CalebO-B/Roll-Only-Canard-Prototype--Controls-Lab-Final-Project-/STL Files/(2in gear) Pinion No edits.STL

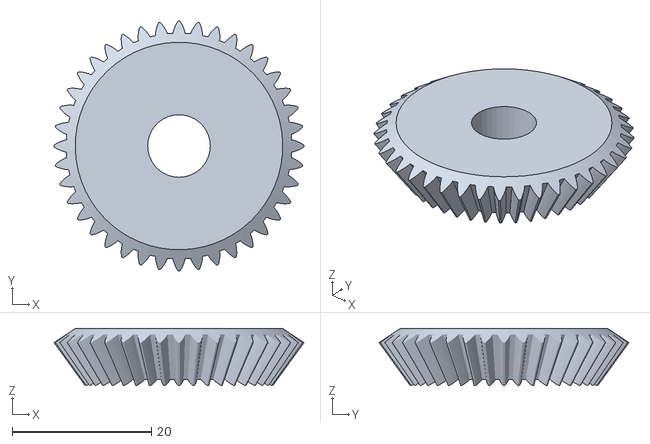
[picture p23: CAD file, 2025-02-27]
STL Files/(2in gear) Pinion No edits.STL
35.9 x 35.9 x 8.20
