CalebO-B/Roll-Only-Canard-Prototype--Controls-Lab-Final-Project-/Solidworks Files/Servo.SLDPRT

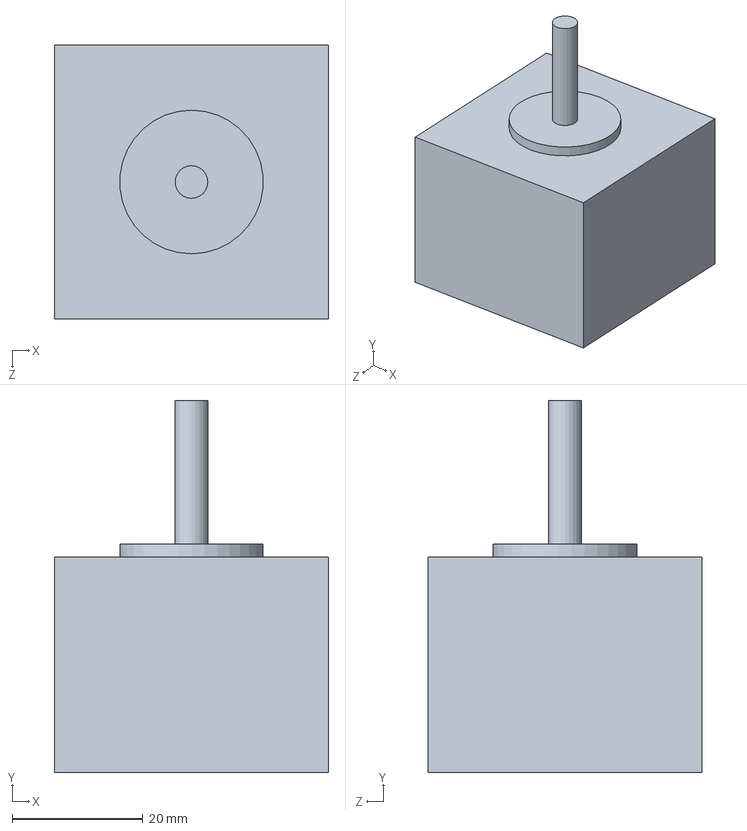
[picture p24: CAD file, 2025-02-27]
Solidworks Files/Servo.SLDPRT
42.0 x 57.0 x 42.0 mm
