CalebO-B/Roll-Only-Canard-Prototype--Controls-Lab-Final-Project-/STL Files/(2in gear) Gear No edits.STL

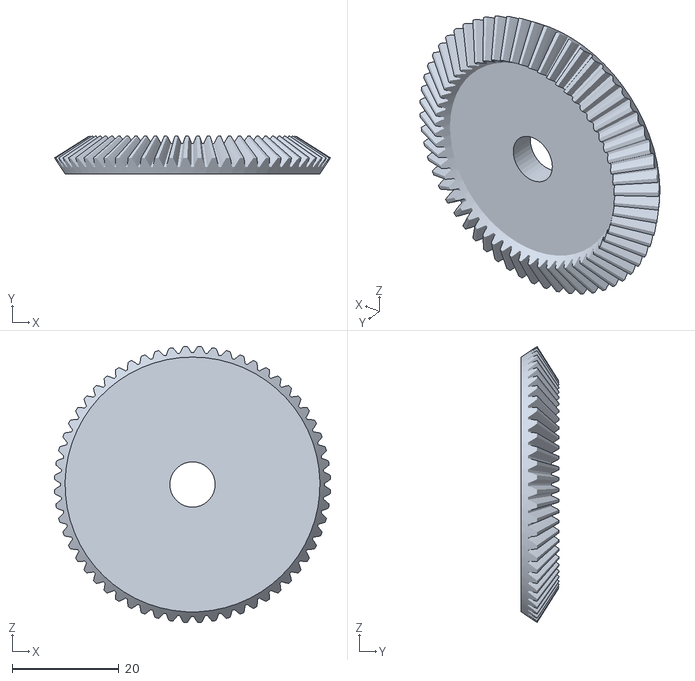
[picture p25: CAD file, 2025-02-27]
STL Files/(2in gear) Gear No edits.STL
51.6 x 7.05 x 51.6
