CalebO-B/Roll-Only-Canard-Prototype--Controls-Lab-Final-Project-/Solidworks Files/Spacer.SLDPRT

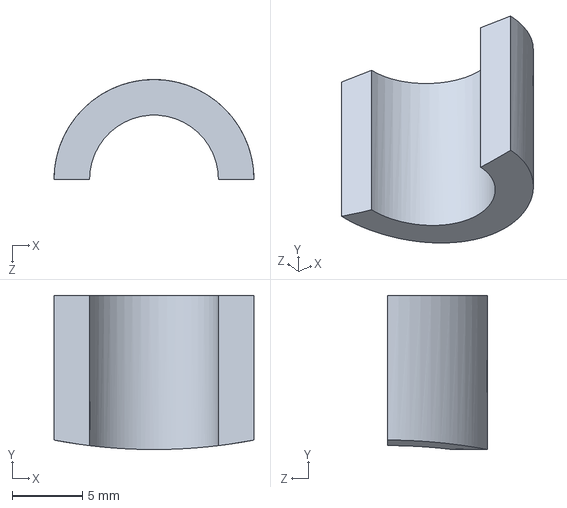
[picture p26: CAD file, 2025-02-27]
Solidworks Files/Spacer.SLDPRT
14.3 x 11.0 x 7.14 mm
