CalebO-B/Roll-Only-Canard-Prototype--Controls-Lab-Final-Project-/STL Files/Mount Test.STL

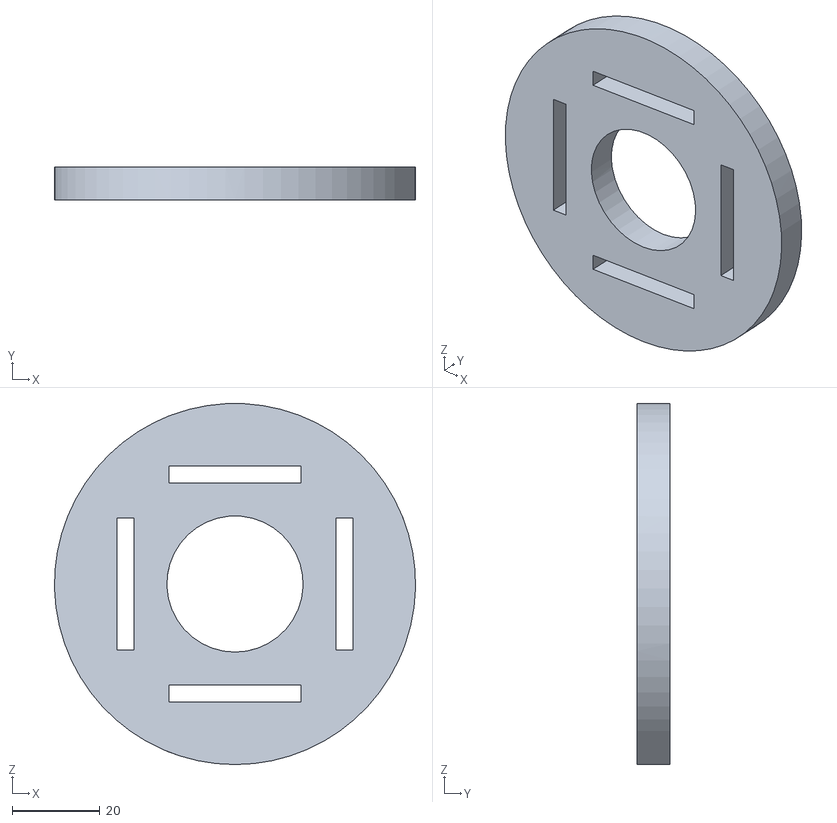
[picture p27: CAD file, 2025-02-27]
STL Files/Mount Test.STL
82.2 x 7.62 x 82.2
